azerimaker/Penguino-SAMR34/Penguino-Photos/03-oshparkPCBsoldered.jpg

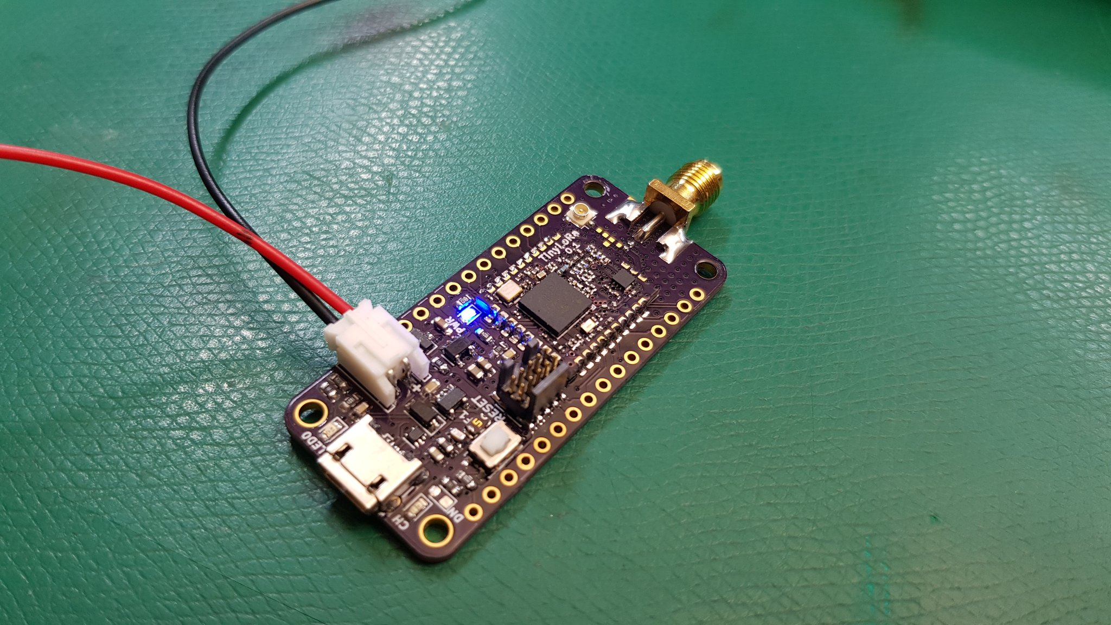
Penguino-Photos/03-oshparkPCBsoldered.jpg
