azerimaker/Penguino-SAMR34/TinyLoRa-Feather-Breakout/TLM-4260-breakout-v1_0/TLM-4260-breakout-v1_0.sch

## KiCad design TinyLoRa-Feather-Breakout/TLM-4260-breakout-v1_0/TLM-4260-breakout-v1_0.sch (2019-11-09)

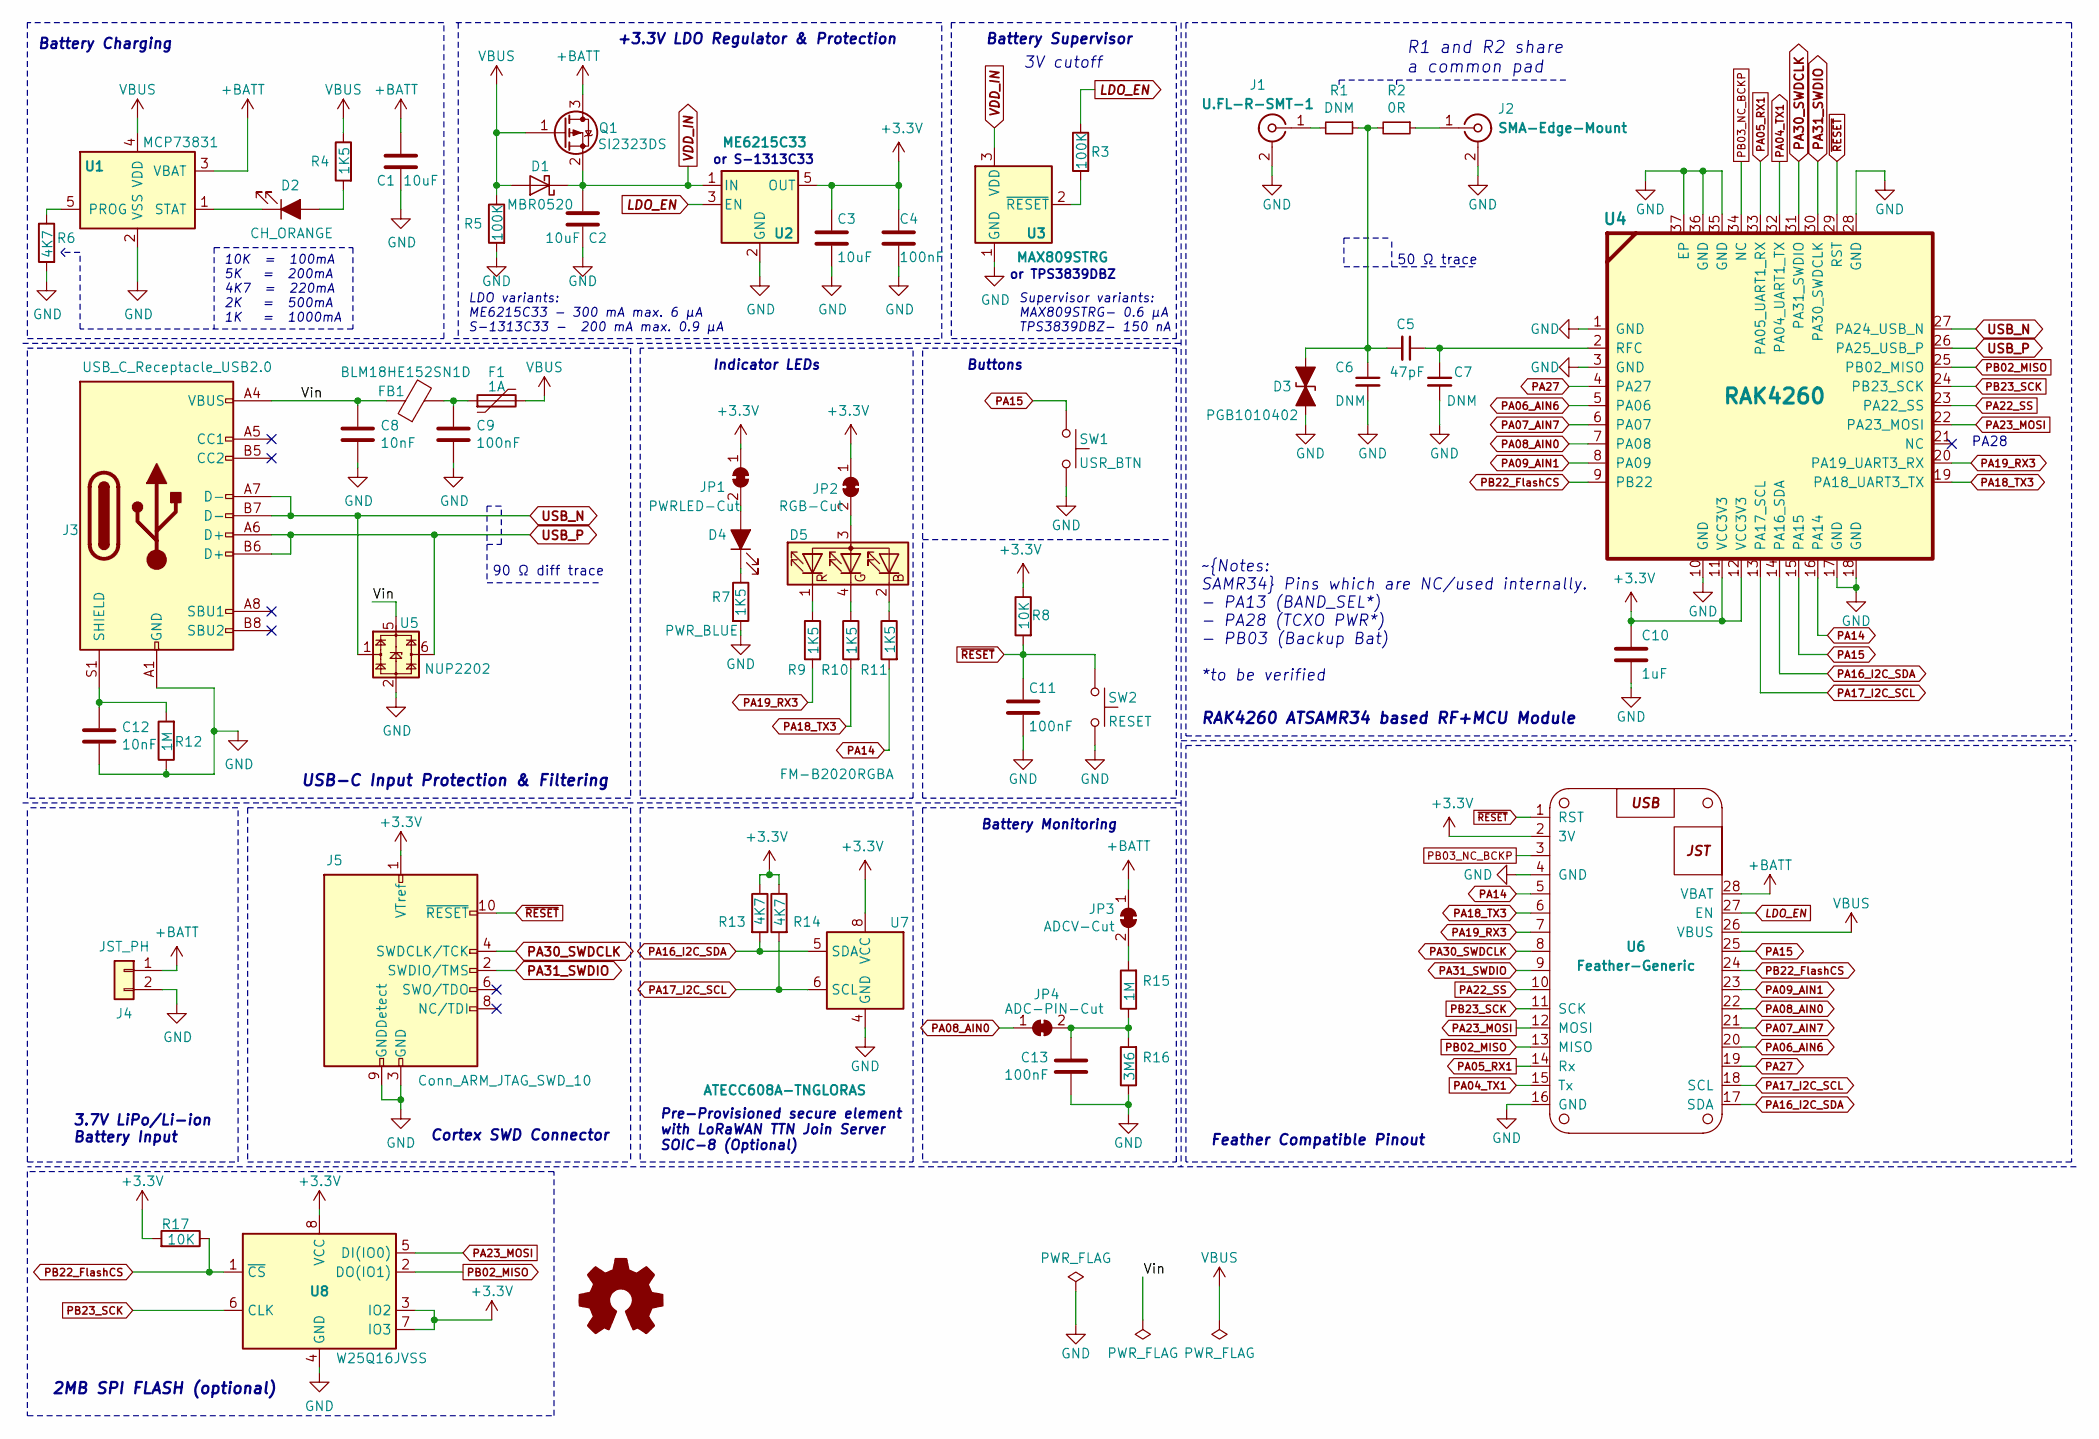
[picture p22: schematic TLM-4260-breakout-v1_0.sch]

Parts:
C1, C2, C3: 10uF; C_0603_1608Metric
C4, C9: 100nF; C_0603_1608Metric; MPN CC0603KRX7R9BB104
C5: 47pF; C_0402_1005Metric
C6, C7: DNM; C_0402_1005Metric
C8, C12: 10nF; C_0603_1608Metric; MPN CC0603KRX7R9BB103
C10: 1uF; C_0603_1608Metric; MPN CC0603KRX7R8BB105
C11, C13: 100nF; C_0402_1005Metric; MPN CC0603KRX7R9BB104
D1: MBR0520; D_SOD-123; MPN MBR0520
D2: CH_ORANGE; LED_0603_1608Metric
D3: PGB1010402; L_0402_1005Metric; MPN PGB1010402KR
D4: PWR_BLUE; LED_0603_1608Metric
D5: FM-B2020RGBA; LED_Cree-PLCC4_2x2mm_CW; MPN FM-B2020RGBA-HG
F1: 1A; Fuse_0805_2012Metric; MPN 0805L110SLYR
FB1: BLM18HE152SN1D; L_0603_1608Metric; MPN BLM18HE152SN1D
J1: U.FL-R-SMT-1; U.FL_Hirose_U.FL-R-SMT-1_Vertical; MPN U.FL-R-SMT-1(80)
J2: SMA-Edge-Mount; SMA_J_P_X_ST_EM1_EdgeMount; MPN SMA-J-P-H-ST-EM1
J3: USB_C_Receptacle_USB2.0; USB_C_Receptacle_Palconn_UTC16-G; MPN TYPE-C-31-M-12
J4: JST_PH; JST_PH_S2B-PH-SM4-TB_1x02-1MP_P2.00mm_Horizontal; MPN S2B-PH-SM4-TB(LF)(SN)
J5: Conn_ARM_JTAG_SWD_10; PinHeader_2x05_P1.27mm_Vertical_SMD
JP1: PWRLED-Cut; SolderJumper-2_P1.3mm_Bridged_RoundedPad1.0x1.5mm
JP2: RGB-Cut; SolderJumper-2_P1.3mm_Bridged_RoundedPad1.0x1.5mm
JP3: ADCV-Cut; SolderJumper-2_P1.3mm_Bridged_RoundedPad1.0x1.5mm
JP4: ADC-PIN-Cut; SolderJumper-2_P1.3mm_Bridged_RoundedPad1.0x1.5mm
Q1: SI2323DS; SOT-23; MPN SI2323DS-T1-E3
R1: DNM; R_0402_1005Metric
R2: 0R; R_0402_1005Metric
R3, R5: 100K; R_0402_1005Metric
R4, R7, R9, R10, R11: 1K5; R_0402_1005Metric
R6, R13, R14: 4K7; R_0402_1005Metric
R8, R17: 10K; R_0402_1005Metric
R12, R15: 1M; R_0402_1005Metric
R16: 3M6; R_0402_1005Metric; MPN RC0402JR-073M6L
SW1: USR_BTN; SW_Push_SKRPACE010; MPN SKRPACE010
SW2: RESET; SW_Push_SKRPACE010; MPN SKRPACE010
U1: MCP73831; SOT-23-5; MPN MCP73831-2-OT
U2: ME6215C33; SOT-23-5; MPN ME6215C33
U3: MAX809STRG; SOT-23; MPN MAX809STRG
U4: RAK4260; RAK4260-footprint_w_solder_paste
U5: NUP2202; SOT-363_SC-70-6; MPN NUP2202W1T2G
U6: Feather-Generic
U7: ATECC608A-TNGLORAS; SOIC-8_3.9x4.9mm_P1.27mm; MPN ATECC608A-TNGLORAS-B
U8: W25Q16JVSS; SOIC-8_5.23x5.23mm_P1.27mm

Connections:
+3.3V: C3.1, C4.1, C10.1, J5.1 (VTref), JP1.1 (A), JP2.1 (A), R8.1, R13.1, R14.1, R17.2, U2.5 (OUT), U4.11 (VCC3V3), U4.12 (VCC3V3), U6.2 (3V), U7.8 (VCC), U8.3 (IO2), U8.7 (IO3), U8.8 (VCC)
+BATT: C1.1, J4.1, JP3.1 (A), Q1.3 (D), U1.3 (VBAT), U6.28 (VBAT)
GND: C1.2, C2.2, C3.2, C4.2, C6.2, C7.2, C8.2, C9.2, C10.2, C11.2, C12.1, C13.1, D3.2 (A2), J1.2 (Ext), J2.2 (Ext), J3.A1 (GND), J3.A12 (GND), J3.B1 (GND), J3.B12 (GND), J4.2, J5.3 (GND), J5.5 (GND), J5.9 (GNDDetect), R5.2, R6.2, R7.2, R12.1, R16.1, SW1.1, SW2.1, U1.2 (VSS), U2.2 (GND), U3.1 (GND), U4.1 (GND), U4.3 (GND), U4.10 (GND), U4.17 (GND), U4.18 (GND), U4.28 (GND), U4.35 (GND), U4.36 (GND), U4.37 (EP), U5.2, U6.4 (GND), U6.16 (GND), U7.4 (GND), U8.4 (GND)
LDO_EN: R3.1, U2.3 (EN), U6.27 (EN)
unnamed: C5.1, C7.1, U4.2 (RFC)
unnamed: C5.2, C6.1, D3.1 (A1), R1.1, R2.2
unnamed: C9.1, F1.1, FB1.2
unnamed: C12.2, J3.S1 (SHIELD), R12.2
unnamed: C13.2, JP4.2 (B), R15.1, R16.2
unnamed: D2.1 (K), U1.1 (STAT)
unnamed: D2.2 (A), R4.2
unnamed: D4.1 (K), R7.1
unnamed: D4.2 (A), JP1.2 (B)
unnamed: D5.1 (RK), R9.1
unnamed: D5.2 (BK), R11.1
unnamed: D5.3 (A), JP2.2 (B)
unnamed: D5.4 (GK), R10.1
unnamed: J1.1 (In), R1.2
unnamed: J2.1 (In), R2.1
unnamed: JP3.2 (B), R15.2
unnamed: R3.2, U3.2 (~RESET)
unnamed: R6.1, U1.5 (PROG)
PA04_TX1: U4.32 (PA04_UART1_TX), U6.15 (Tx)
PA05_RX1: U4.33 (PA05_UART1_RX), U6.14 (Rx)
PA06_AIN6: U4.5 (PA06), U6.20
PA07_AIN7: U4.6 (PA07), U6.21
PA08_AIN0: JP4.1 (A), U4.7 (PA08), U6.22
PA09_AIN1: U4.8 (PA09), U6.23
PA14: R11.2, U4.16 (PA14), U6.5
PA15: SW1.2, U4.15 (PA15), U6.25
PA16_I2C_SDA: R13.2, U4.14 (PA16_SDA), U6.17 (SDA), U7.5 (SDA)
PA17_I2C_SCL: R14.2, U4.13 (PA17_SCL), U6.18 (SCL), U7.6 (SCL)
PA18_TX3: R10.2, U4.19 (PA18_UART3_TX), U6.6
PA19_RX3: R9.2, U4.20 (PA19_UART3_RX), U6.7
PA22_SS: U4.23 (PA22_SS), U6.10
PA23_MOSI: U4.22 (PA23_MOSI), U6.12 (MOSI), U8.5 (DI(IO0))
PA27: U4.4 (PA27), U6.19
PA30_SWDCLK: J5.4 (SWDCLK/TCK), U4.31 (PA31_SWDIO), U6.8
PA31_SWDIO: J5.2 (SWDIO/TMS), U4.30 (PA30_SWDCLK), U6.9
PB02_MISO: U4.25 (PB02_MISO), U6.13 (MISO), U8.2 (DO(IO1))
PB03_NC_BCKP: U4.34 (NC), U6.3
PB22_FlashCS: R17.1, U4.9 (PB22), U6.24, U8.1 (~CS)
PB23_SCK: U4.24 (PB23_SCK), U6.11 (SCK), U8.6 (CLK)
USB_N: J3.A7 (D-), J3.B7 (D-), U4.27 (PA24_USB_N), U5.1
USB_P: J3.A6 (D+), J3.B6 (D+), U4.26 (PA25_USB_P), U5.6
VBUS: D1.2 (A), F1.2, Q1.1 (G), R4.1, R5.1, U1.4 (VDD), U6.26 (VBUS)
VDD_IN: C2.1, D1.1 (K), Q1.2 (S), U2.1 (IN), U3.3 (VDD)
Vin: C8.1, FB1.1, J3.A4 (VBUS), J3.A9 (VBUS), J3.B4 (VBUS), J3.B9 (VBUS), U5.5
~RESET: C11.1, J5.10 (~RESET~), R8.2, SW2.2, U4.29 (RST), U6.1 (RST)

Notes on the sheet:
10K = 100mA 5K = 200mA 4K7 = 220mA 2K = 500mA 1K = 1000mA
3.7V LiPo/Li-ion Battery Input
Battery Charging
USB-C Input Protection & Filtering
Indicator LEDs
RAK4260 ATSAMR34 based RF+MCU Module
Feather Compatible Pinout
Battery Monitoring
R1 and R2 share a common pad
Cortex SWD Connector
90 Ω diff trace
50 Ω trace
~Notes: SAMR34 Pins which are NC/used internally. - PA13 (BAND_SEL*) - PA28 (TCXO PWR*) - PB03 (Backup Bat) *to be verified
PA28
Pre-Provisioned secure element with LoRaWAN TTN Join Server SOIC-8 (Optional)
Buttons
+3.3V LDO Regulator & Protection
Battery Supervisor
LDO variants: ME6215C33 - 300 mA max. 6 μA S-1313C33 - 200 mA max. 0.9 μA
3V cutoff
or TPS3839DBZ
or S-1313C33
Supervisor variants: MAX809STRG- 0.6 μA TPS3839DBZ- 150 nA
2MB SPI FLASH (optional)
